jamesmarrs/farseer/out/im-fig31-minimal.png

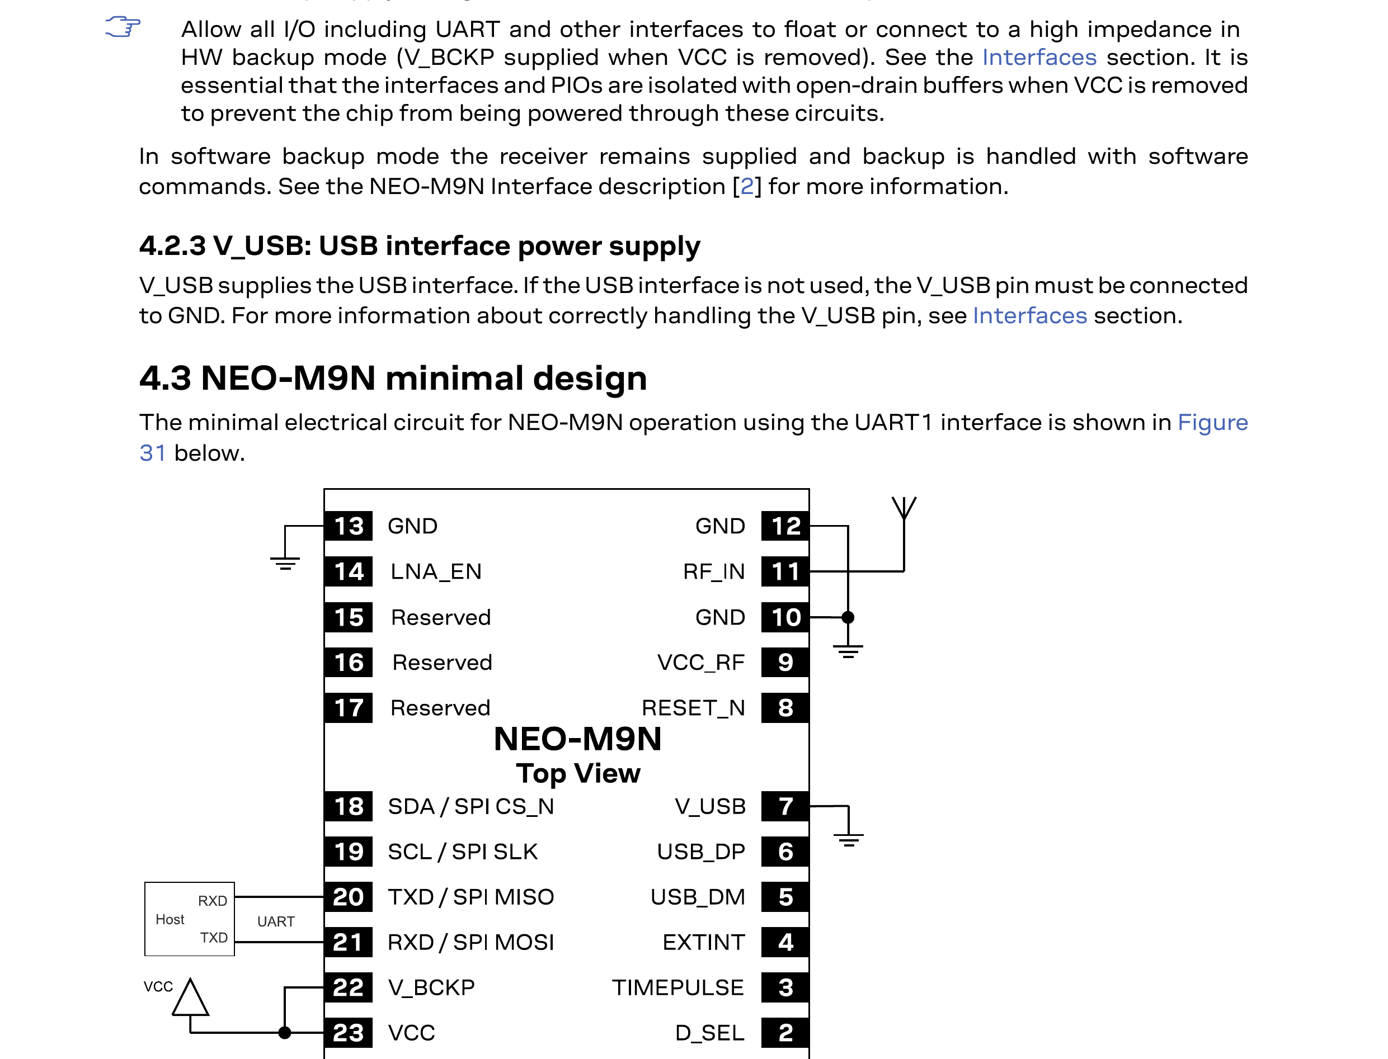
out/im-fig31-minimal.png
