jamesmarrs/farseer/out/im-fig39-rf.png

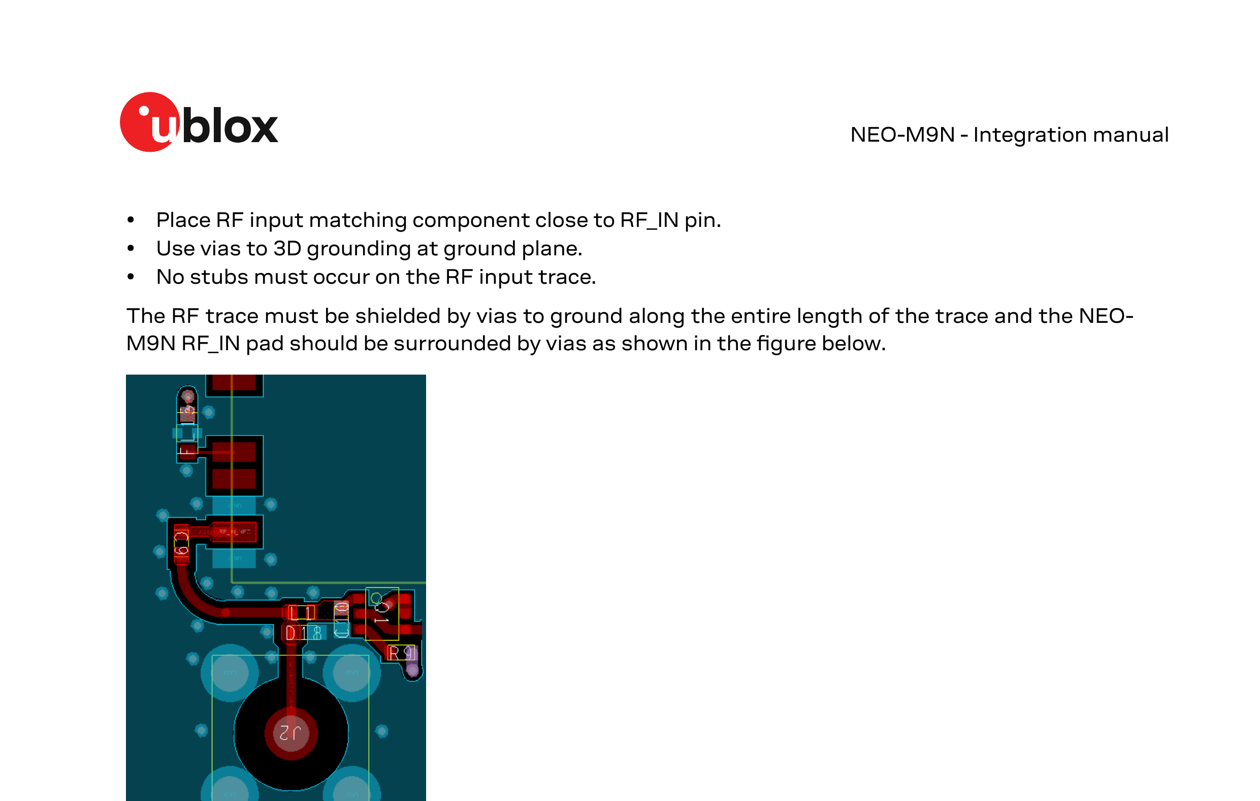
out/im-fig39-rf.png
