jamesmarrs/farseer/out/im-fig40-b.png

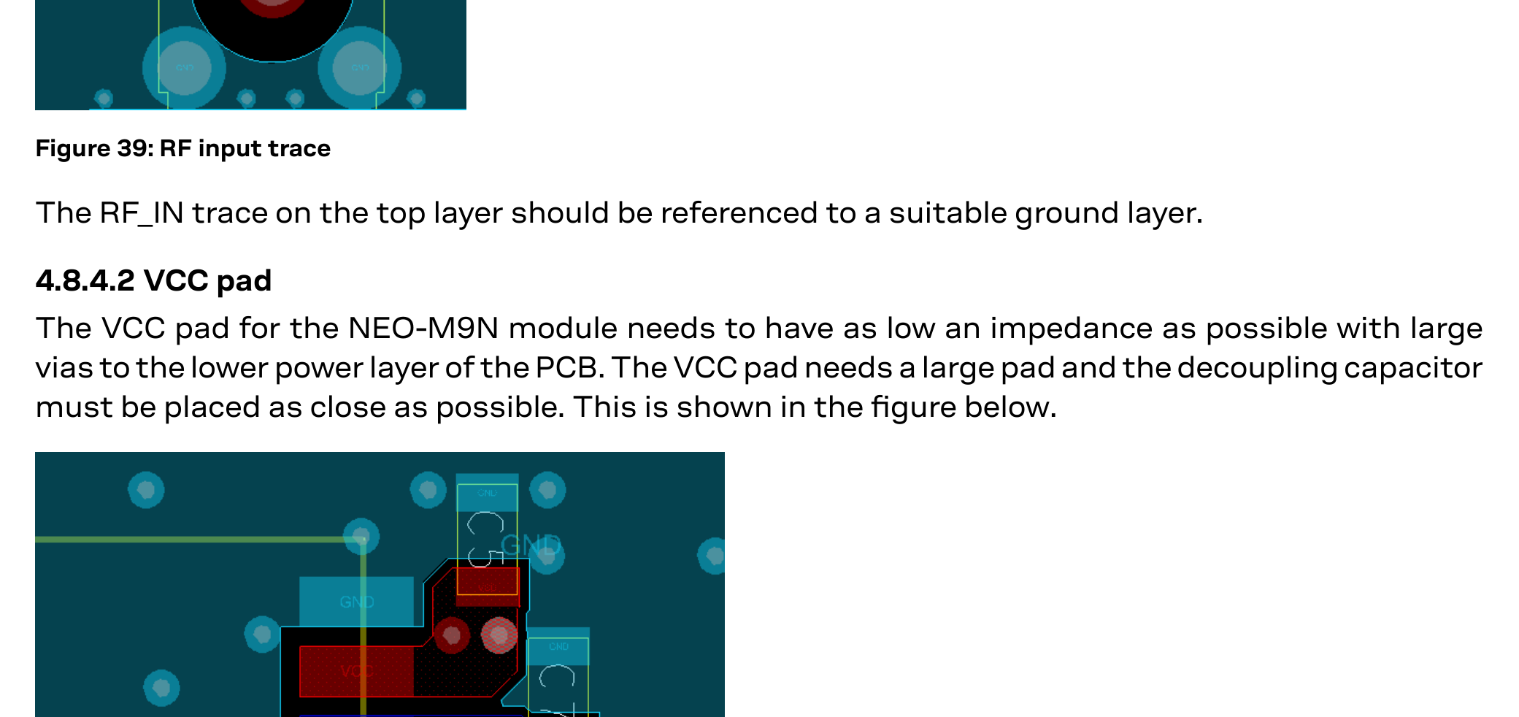
out/im-fig40-b.png
