jamesmarrs/farseer/out/im-fig40-vcc.png

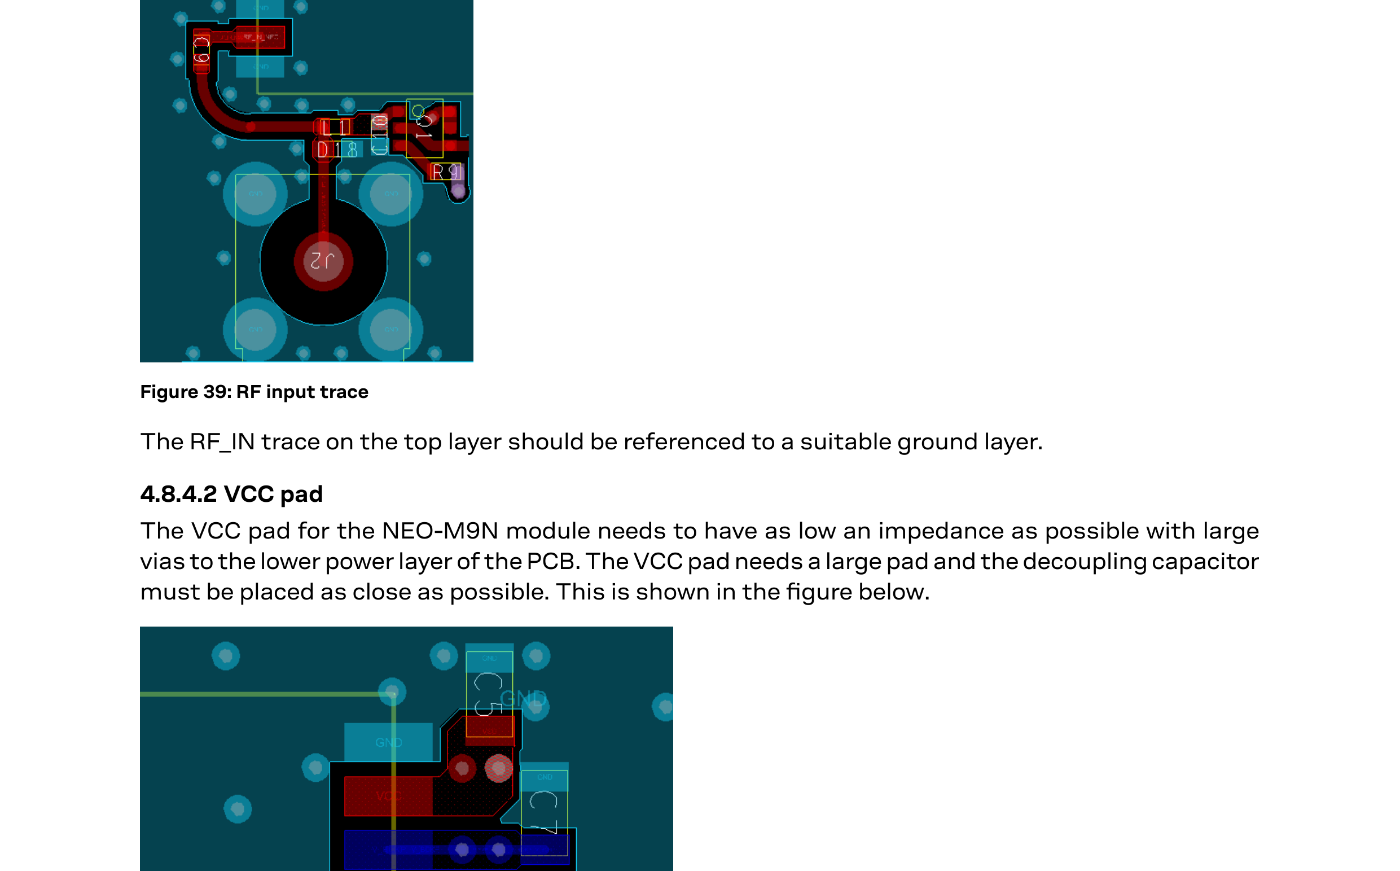
out/im-fig40-vcc.png
