jamesmarrs/farseer/out/j5-model-check.png

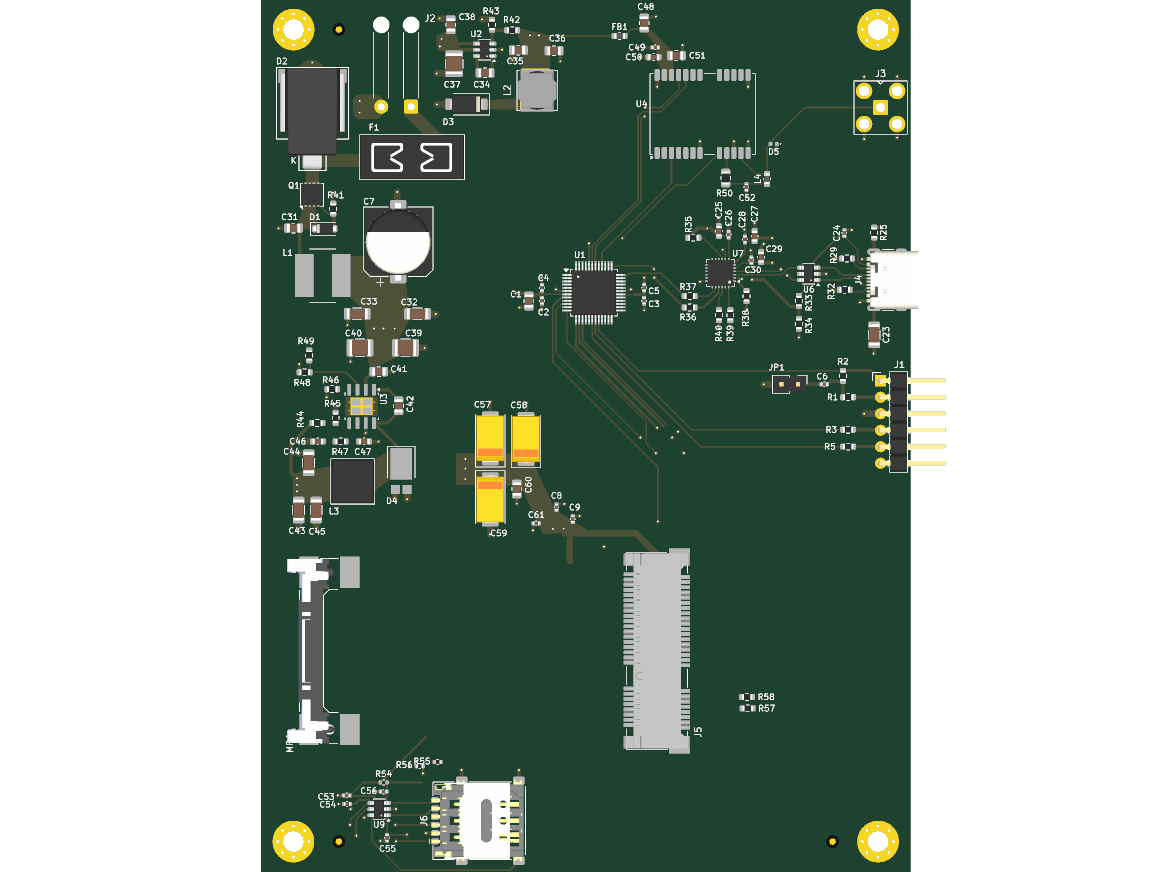
out/j5-model-check.png
