jamesmarrs/farseer/out/p71-71.png

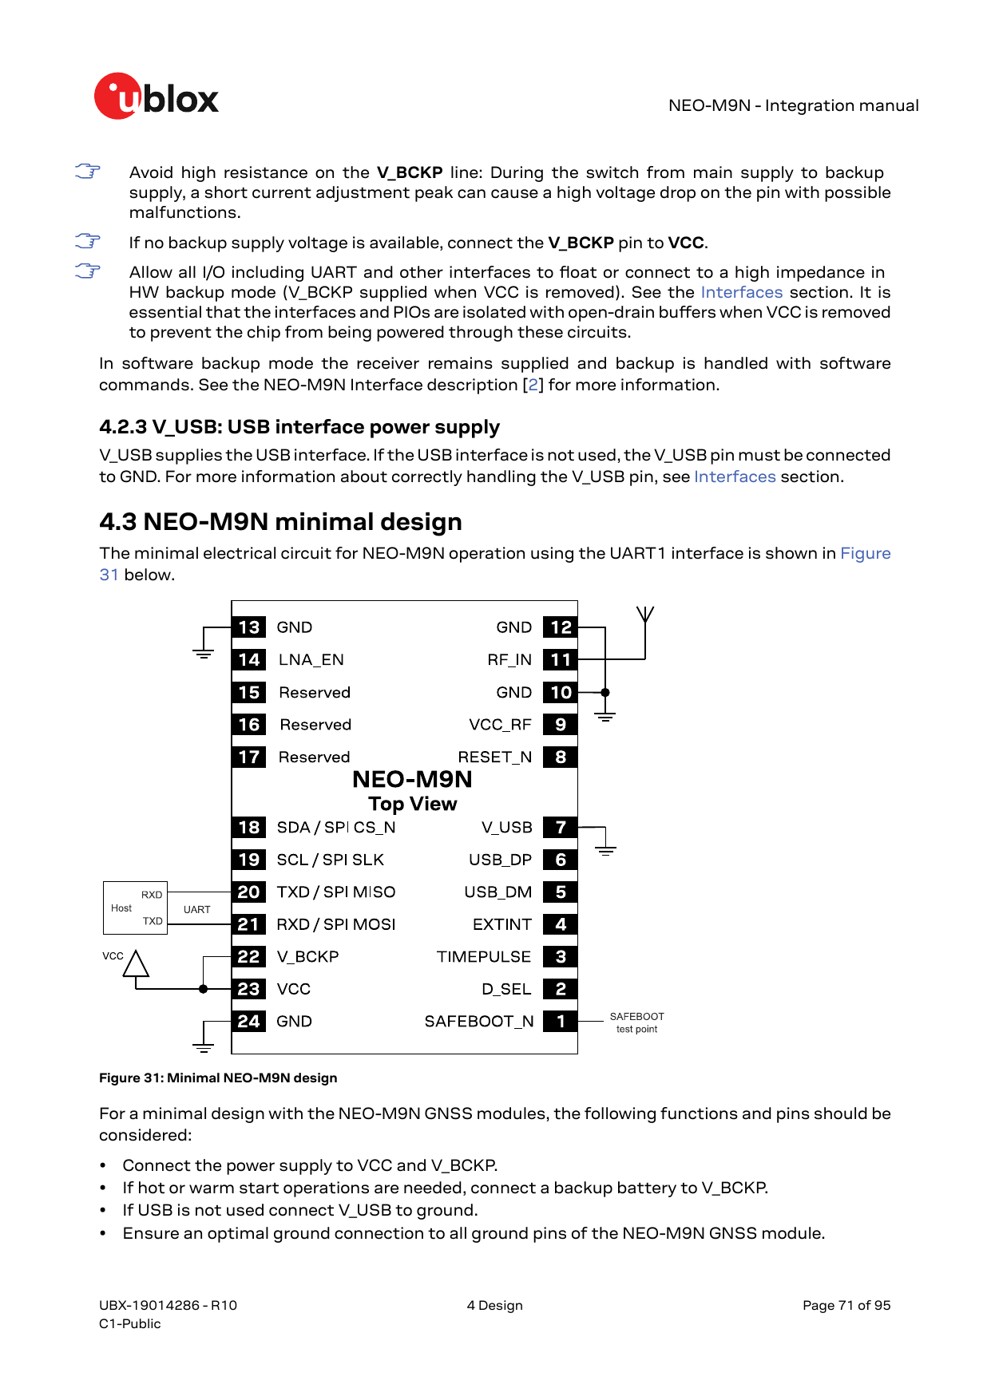
out/p71-71.png
